ginofco/Pancho_4/2_Design/22_TinkerCAD/P4_Braco.stl

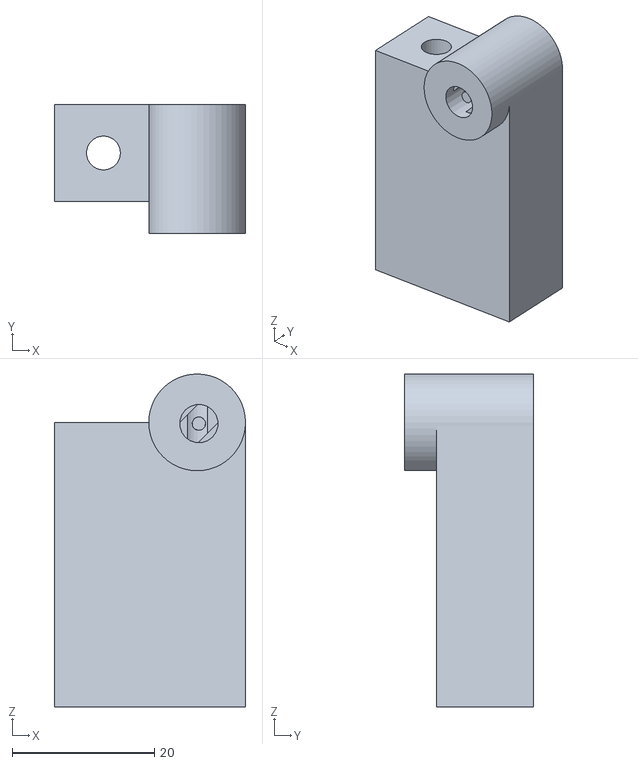
[picture p15: CAD file, 2026-04-18, an earlier design]
2_Design/22_TinkerCAD/P4_Braco.stl
26.9 x 18.1 x 46.8
