ginofco/Pancho_4/2_Design/22_TinkerCAD/P4_SuporteStopBraco.stl

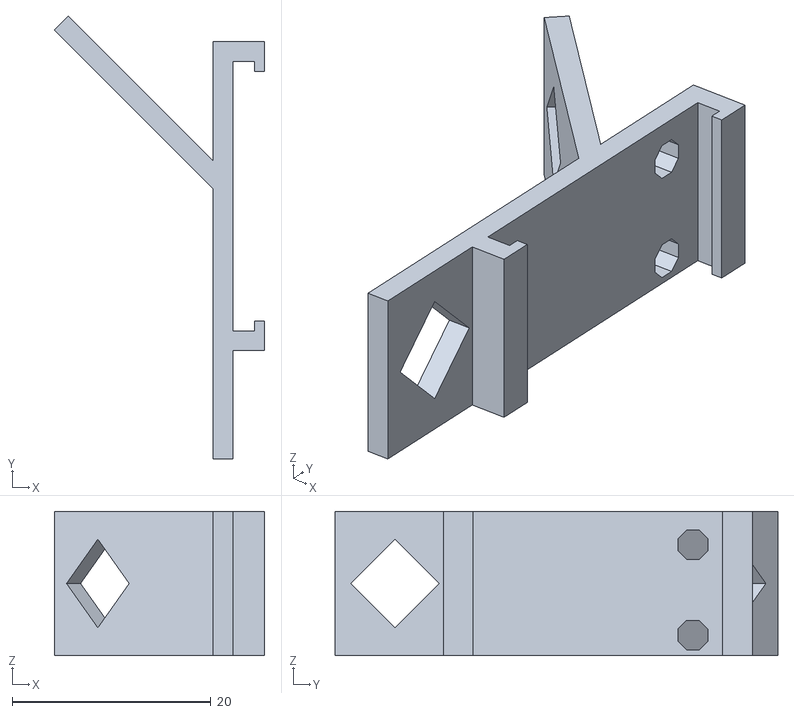
[picture p16: CAD file, 2026-04-18, an earlier design]
2_Design/22_TinkerCAD/P4_SuporteStopBraco.stl
21.1 x 44.6 x 14.5
