ginofco/Pancho_4/2_Design/22_TinkerCAD/P4_SuporteBraco.stl

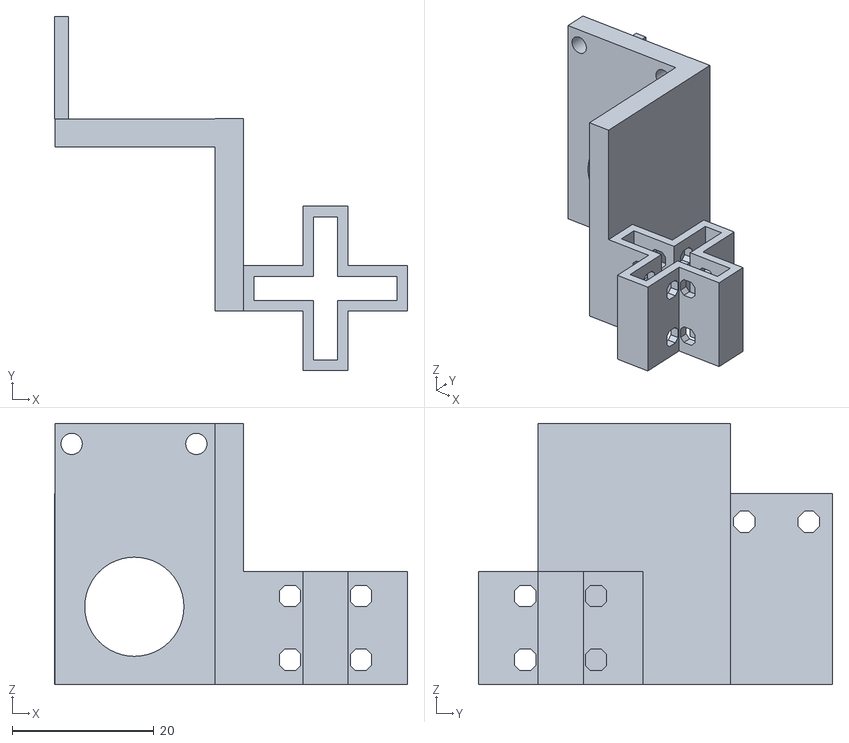
[picture p17: CAD file, 2026-04-18, an earlier design]
2_Design/22_TinkerCAD/P4_SuporteBraco.stl
49.9 x 50.0 x 36.9
